DivCurl/DivRGBCube/Pics/Board-1.jpg

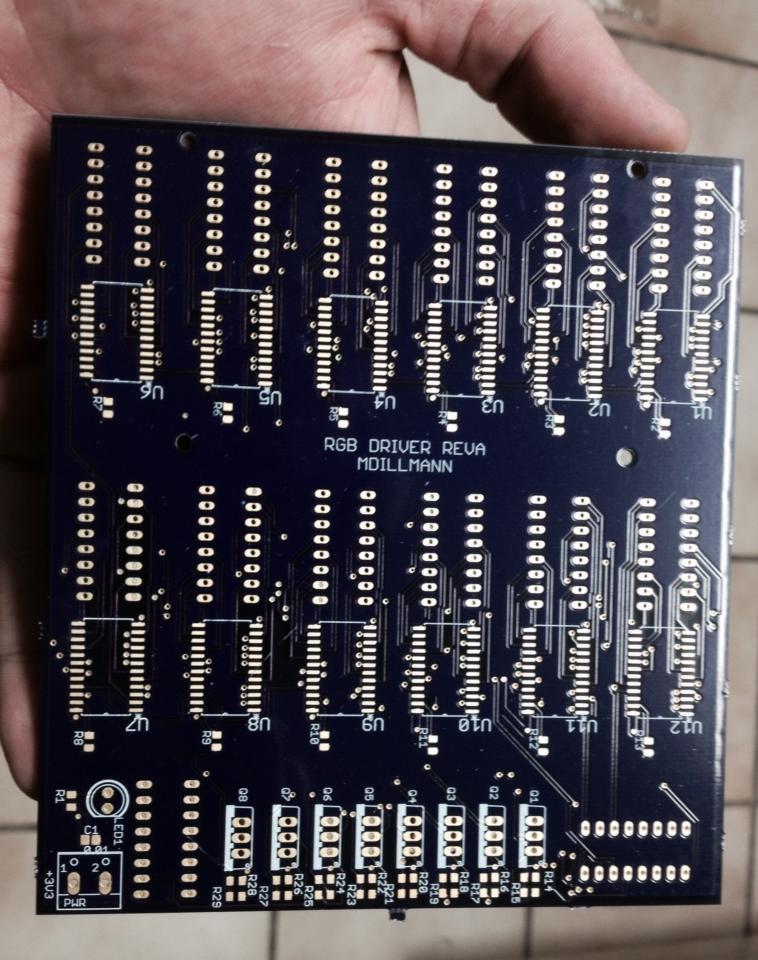
Pics/Board-1.jpg
