DivCurl/DivRGBCube/Pics/Board-2.jpg

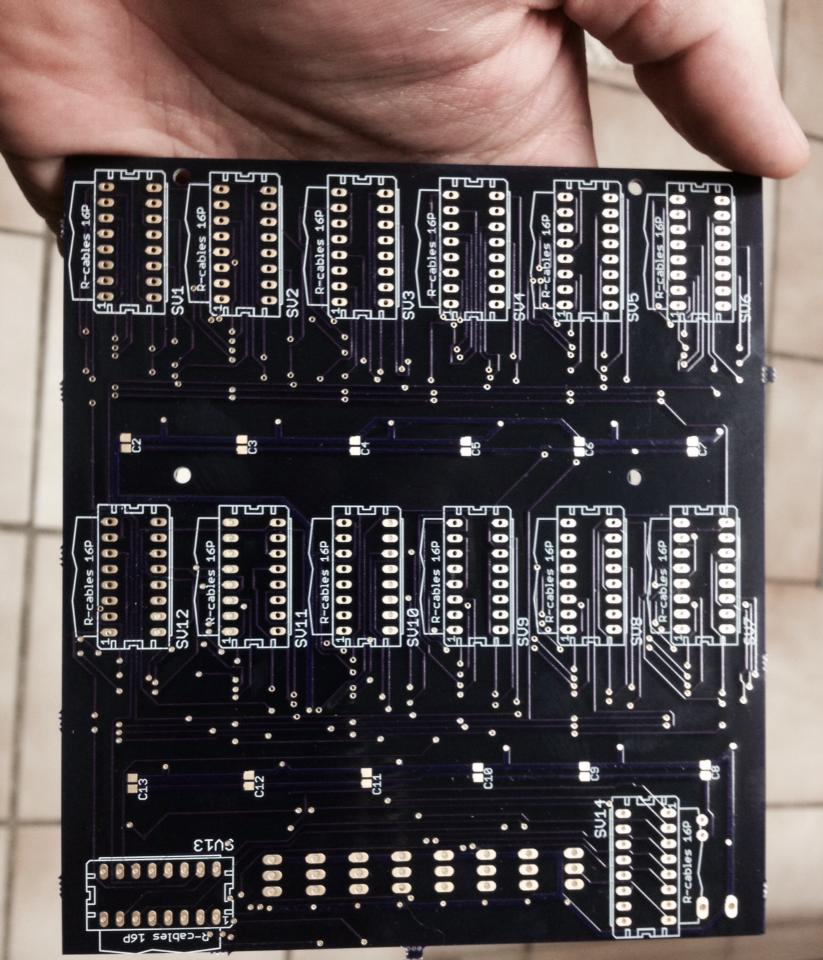
Pics/Board-2.jpg
