DivCurl/DivRGBCube/Pics/Box-2.jpg

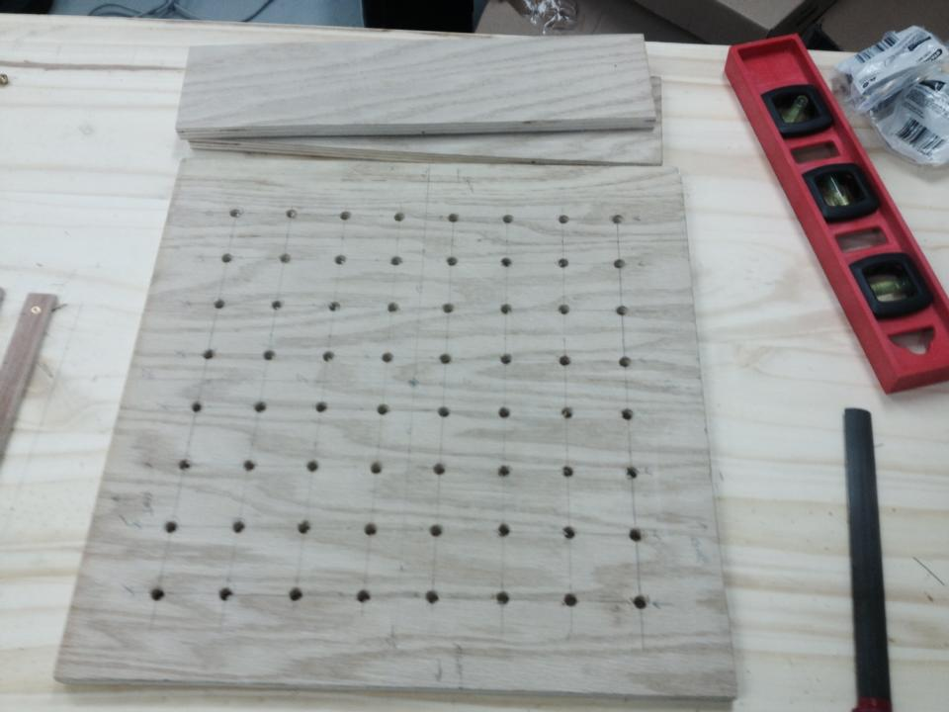
Pics/Box-2.jpg
