DivCurl/DivRGBCube/Pics/Box-3.jpg

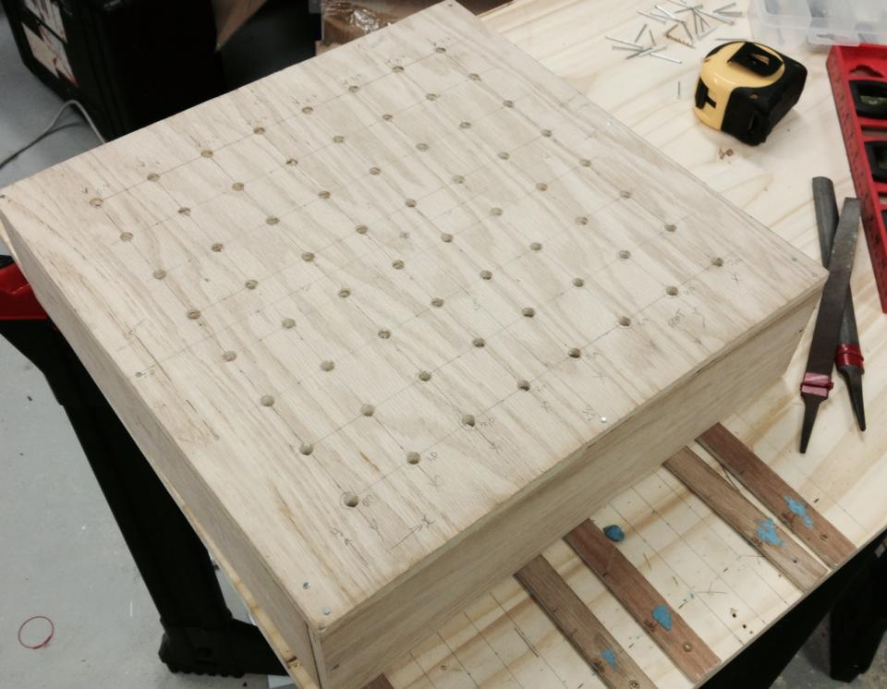
Pics/Box-3.jpg
