DivCurl/DivRGBCube/Pics/Box-4.jpg

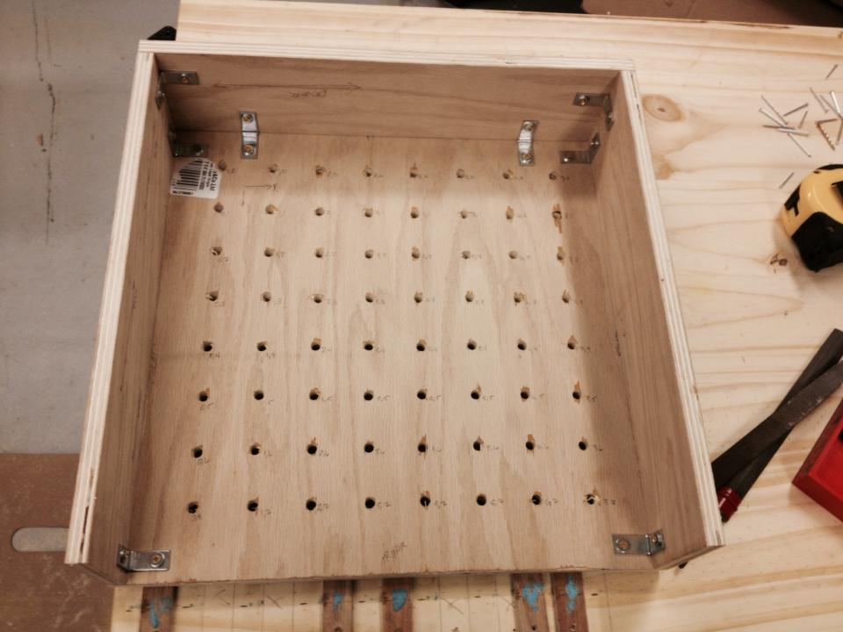
Pics/Box-4.jpg
