DivCurl/DivRGBCube/Pics/Cube-2.jpg

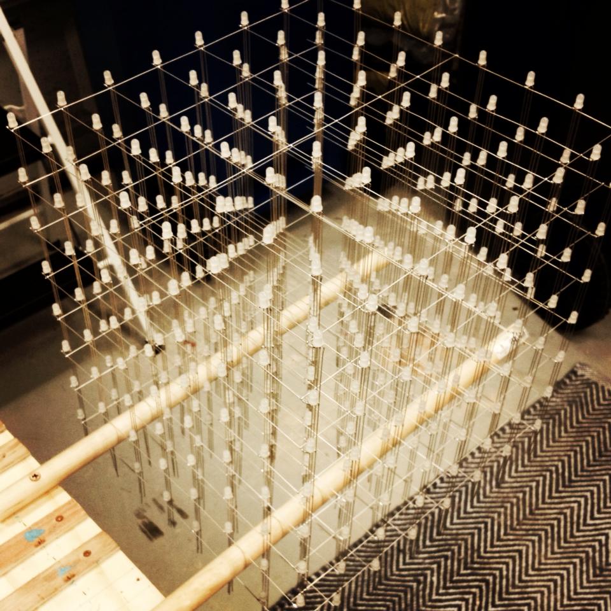
Pics/Cube-2.jpg
