DivCurl/DivRGBCube/Pics/Cube-3.jpg

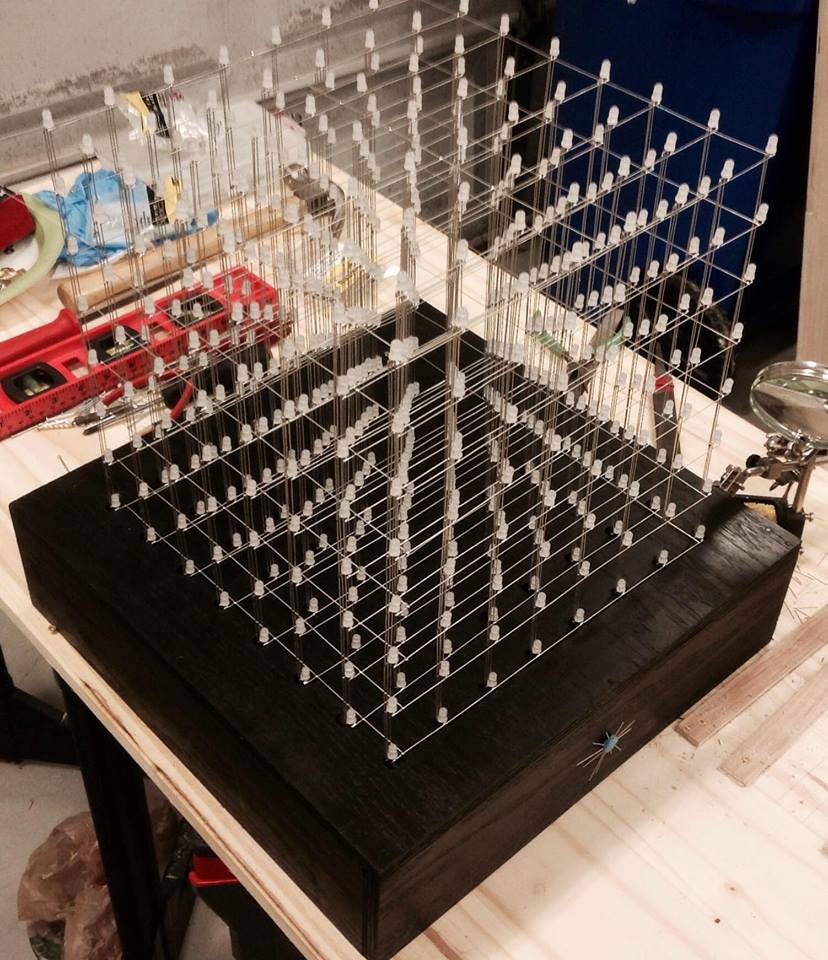
Pics/Cube-3.jpg
