DivCurl/DivRGBCube/Pics/Jig-2.jpg

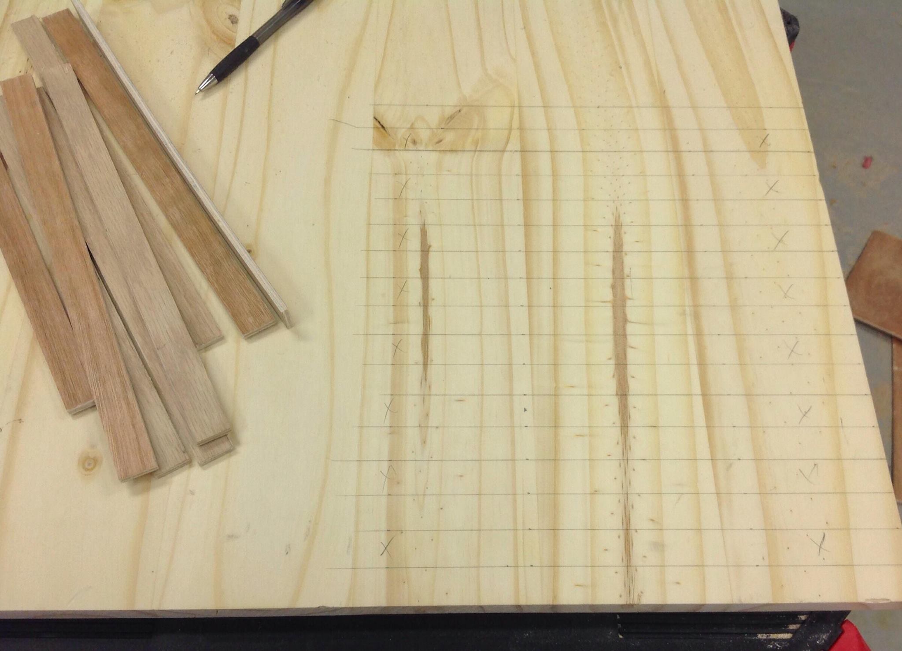
Pics/Jig-2.jpg
