DivCurl/DivRGBCube/Pics/Jig-3.jpg

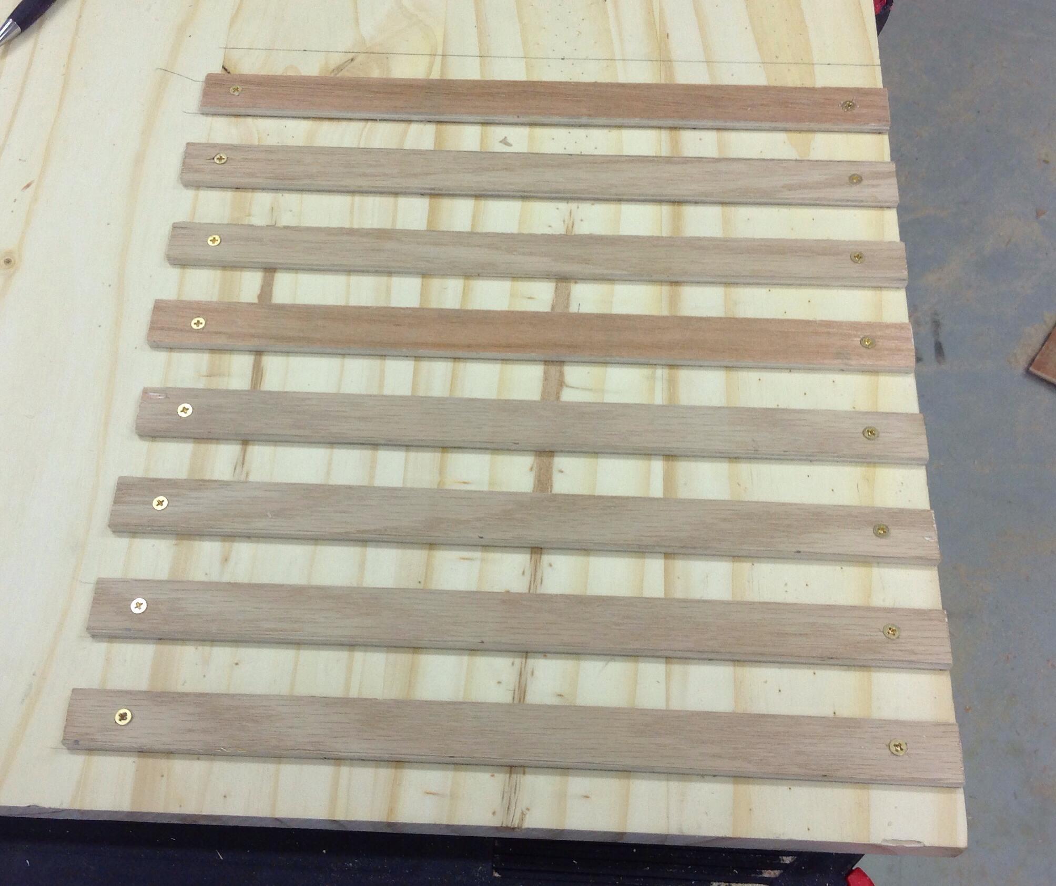
Pics/Jig-3.jpg
