DivCurl/DivRGBCube/Pics/Jig-4.jpg

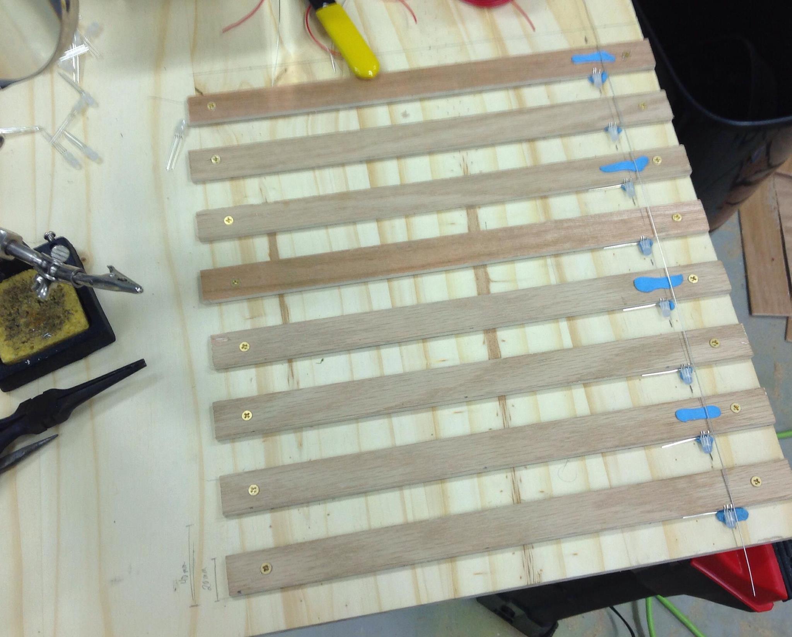
Pics/Jig-4.jpg
