DivCurl/DivRGBCube/Pics/Jig-5.jpg

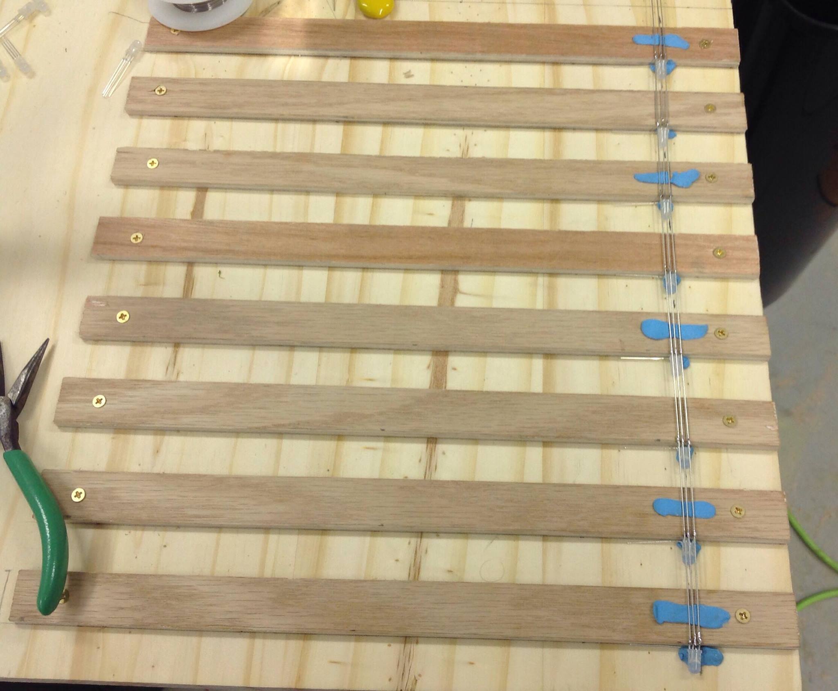
Pics/Jig-5.jpg
