DivCurl/DivRGBCube/Pics/Jig-6.jpg

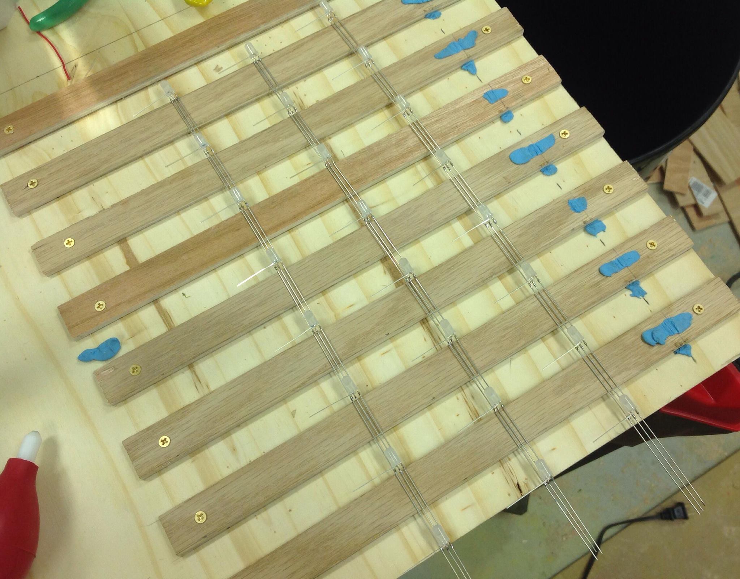
Pics/Jig-6.jpg
