DivCurl/DivRGBCube/Pics/Post-2.jpg

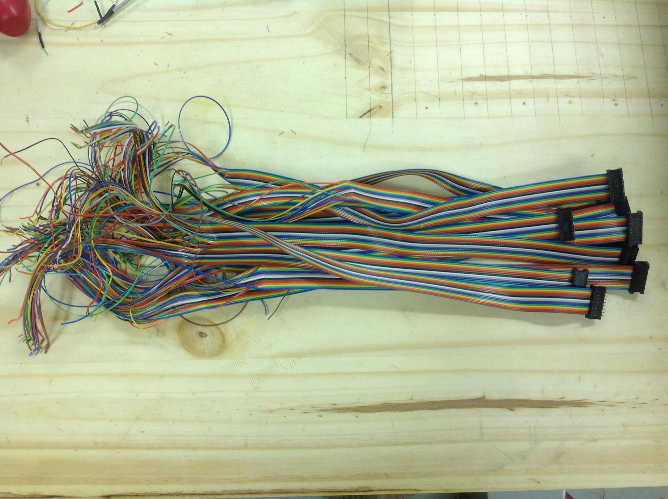
Pics/Post-2.jpg
