DivCurl/DivRGBCube/Pics/Post-3.jpg

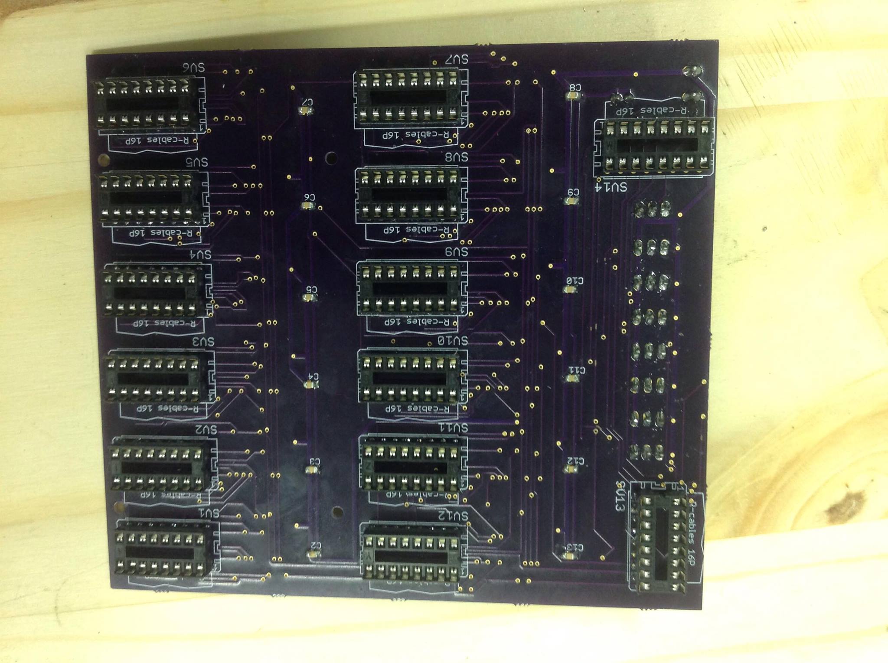
Pics/Post-3.jpg
