DivCurl/DivRGBCube/Pics/Post-4.jpg

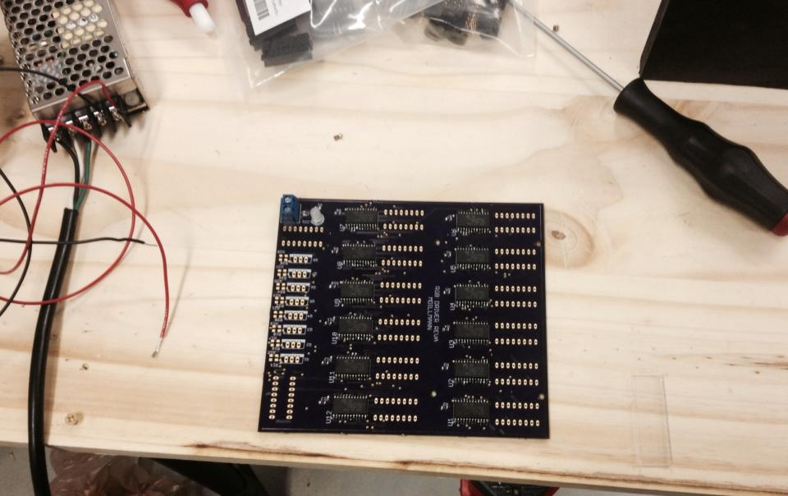
Pics/Post-4.jpg
