DivCurl/DivRGBCube/Pics/Post-5.jpg

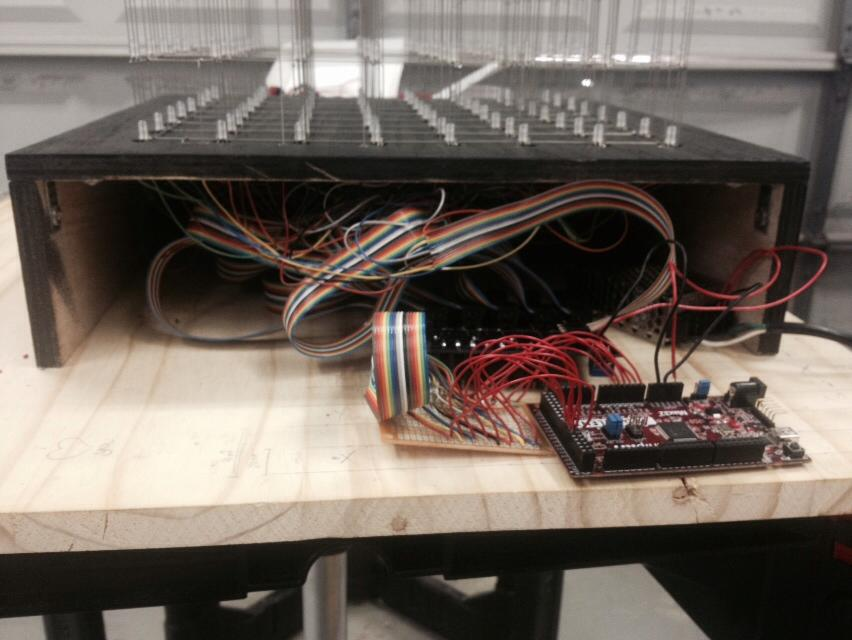
Pics/Post-5.jpg
