DivCurl/DivRGBCube/Pics/Prep-1.jpg

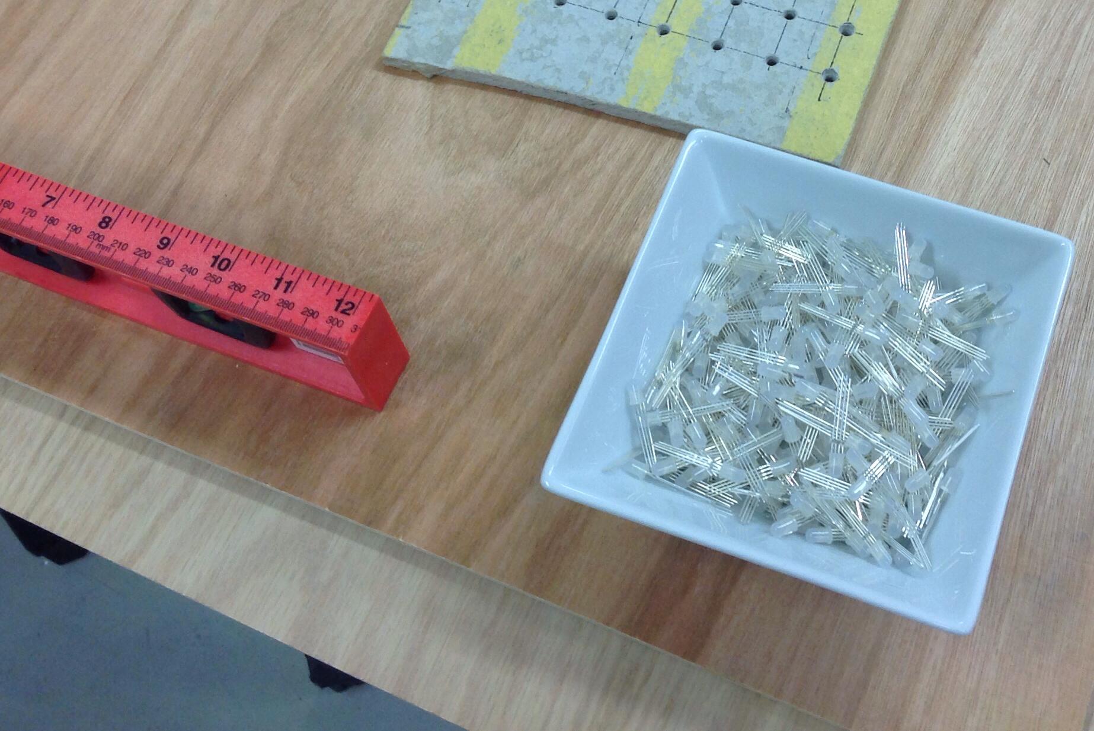
Pics/Prep-1.jpg
