DivCurl/DivRGBCube/Code (PIC32)/0.98/src/matrix.c

#include "../include/matrix.h"
#include "../include/vector.h"

/*
===================
 Name

 Desc
===================
*/
MATRIX4 M_Mul4(MATRIX4 mx1, MATRIX4 mx2) {
    MATRIX4 tmpMx;
    uint8 row, col;

    for (row = 0; row < 4; row++) {
        for (col = 0; col < 4; col++) {
            // since matrix is stored as 1D array, offset column by 4 on
            // each iteration count to ensure columns line up
            tmpMx.mx[col * 4 + row] =
                mx1.mx[0 + row] * mx2.mx[0 + col * 4] +
                mx1.mx[4 + row] * mx2.mx[1 + col * 4] +
                mx1.mx[8 + row] * mx2.mx[2 + col * 4] +
                mx1.mx[12 + row] * mx2.mx[3 + col * 4];
        }
    }
    return tmpMx;
}

/*
===================
 Name

 Desc
===================
*/
MATRIX4 M_Add4(MATRIX4 mx1, MATRIX4 mx2) {
    MATRIX4 tmpMx;
    uint8 i;
    for (i = 0; i < 16; i++)
        tmpMx.mx[i] = mx1.mx[i] + mx2.mx[i];

    return tmpMx;
}

/*
===================
 Name

 Desc
===================
*/
MATRIX4 M_MulScalar4(MATRIX4 inMx, float s) {
    uint8 i;
    for (i = 0; i < 16; i++)
        inMx.mx[i] *= s;

    return inMx;
}

/*
===================
 Name

 Desc
===================
*/
MATRIX4 M_DivScalar4(MATRIX4 inMx, float s) {
    uint8 i;
    for (i = 0; i < 16; i++)
        inMx.mx[i] /= s;

    return inMx;
}

/*
 * | 1 0 0 0 |
 * | 0 1 0 0 |
 * | 0 0 1 0 |
 * | 0 0 0 1 |
 *
 */

/*
===================
 Name

 Desc
===================
*/
void M_Identity4(MATRIX4 *mxptr) {
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
*/
MATRIX3 M_Rotate2D(float theta) {
    MATRIX3 mxTmp;
    // Make an identity matrix first
    M_Identity3(&mxTmp);

    mxTmp.mx[0] = D_Round(cos(theta));
    mxTmp.mx[1] = D_Round(sin(theta));
    mxTmp.mx[3] = D_Round(-sin(theta));
    mxTmp.mx[4] = D_Round(cos(theta));

    return mxTmp;
}

// Working, more testing reqd.
// Noticed limitations due to cube 'display' resolution being fairly low,
// complex objects don't look too hot when rotated through fractional angles
/*
===================
 Name

 Desc
===================
*/
MATRIX4 M_Rotate3D(float alpha, float beta, float gamma) {
    MATRIX4 mxTmp;
    M_Identity4(&mxTmp);

    mxTmp.mx[0] = D_Round(cos(beta)*cos(gamma));
    mxTmp.mx[1] = D_Round(cos(beta)*sin(gamma));
    mxTmp.mx[2] = D_Round(-sin(beta));

    mxTmp.mx[4] = D_Round((cos(gamma)*sin(alpha)*sin(beta)) - (cos(alpha)*sin(gamma)));
    mxTmp.mx[5] = D_Round((cos(alpha)*cos(gamma)) + (sin(alpha)*sin(beta)*sin(gamma)));
    mxTmp.mx[6] = D_Round((cos(beta)*sin(alpha)));

    mxTmp.mx[8] = D_Round((cos(alpha)*cos(gamma)*sin(beta)) + (sin(alpha)*sin(gamma)));
    mxTmp.mx[9] = D_Round((-cos(gamma)*sin(alpha)) + cos(alpha)*sin(beta)*sin(gamma));
    mxTmp.mx[10] = D_Round(cos(alpha)*cos(beta));

    return mxTmp;
}

/*  | 0 3 6 |   | 0 |
 *  | 1 4 7 | * | 1 |
 *  | 2 5 8 |   | 2 |
 */
// Multiply 3X3 matrix by 3x1 VECTOR. Returns 3x1 Vector
// Working
/*
===================
 Name

 Desc
===================
*/
VECTOR3 M_MulVec2D(MATRIX3 mx, VECTOR3 vec) {
    VECTOR3 ptVec;
    int row;
    for (row = 0; row < 3; row++) {
        ptVec.vec[row] =
            mx.mx[0 + row] * vec.vec[0] +
            mx.mx[3 + row] * vec.vec[1] +
            mx.mx[6 + row] * vec.vec[2];
    }
    return ptVec;
}

// Multiply 4X4 matrix by 4x1 VECTOR. Returns 4x1 vector
// Working
/*
===================
 Name

 Desc
===================
*/
VECTOR4 M_MulVec3D(MATRIX4 mx, VECTOR4 vec) {
    VECTOR4 ptVec;
    int row;
    for (row = 0; row < 4; row++) {
        ptVec.vec[row] =
            mx.mx[0 + row] * vec.vec[0] +
            mx.mx[4 + row] * vec.vec[1] +
            mx.mx[8 + row] * vec.vec[2] +
            mx.mx[12 + row] * vec.vec[3];
    }
    return ptVec;
}
